bluthen/isadore_electronics/sensor_unit_modules/thermocoupleMv2/out/thermocoupleMv2.10-pin1s.png

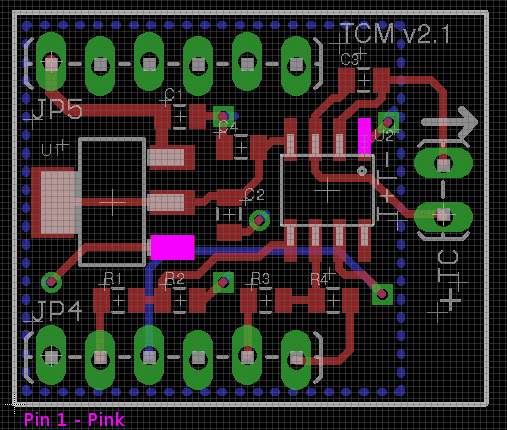
sensor_unit_modules/thermocoupleMv2/out/thermocoupleMv2.10-pin1s.png
