bluthen/isadore_electronics/sensor_unit_bme280/gerbers/sensor_unit_bme280v5.10_assembled_picture.jpg

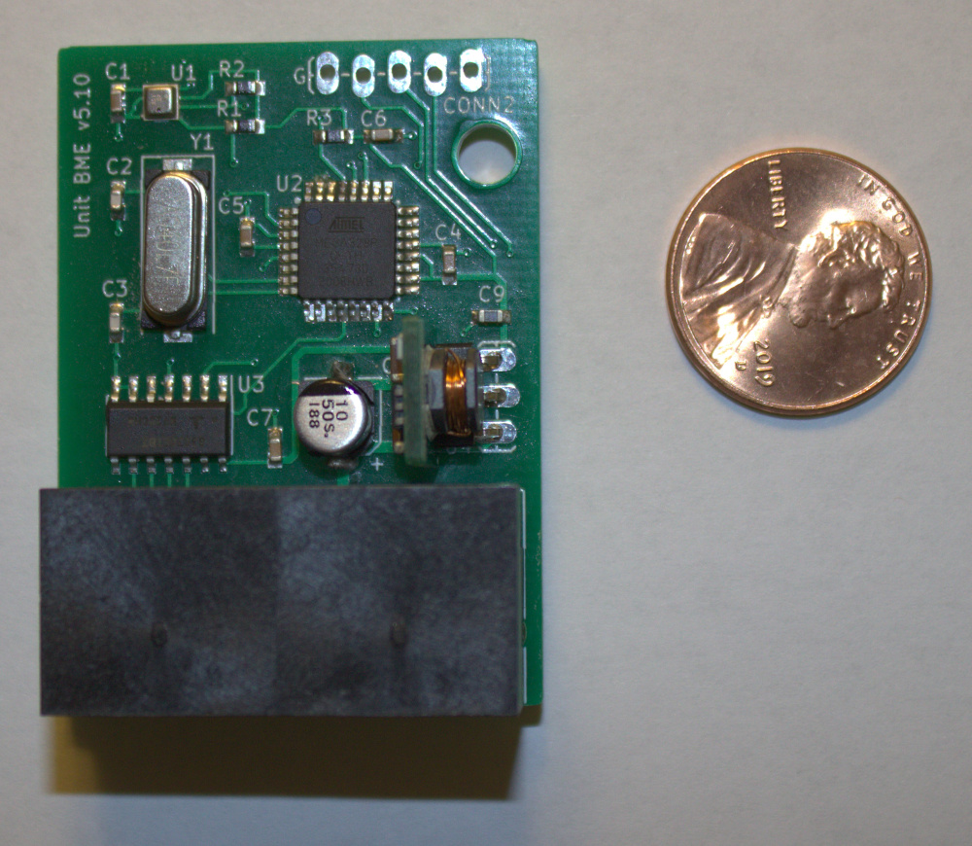
sensor_unit_bme280/gerbers/sensor_unit_bme280v5.10_assembled_picture.jpg
