bluthen/isadore_electronics/dryermaster/spitest.py

import pydev

#!/usr/bin/env python
#
# Bitbang'd SPI interface with an MCP3008 ADC device
# MCP3008 is 8-channel 10-bit analog to digital converter
#  Connections are:
#     CLK => SCLK  
#     DOUT =>  MISO
#     DIN => MOSI
#     CS => CE0

import time
import sys
import spidev
from RPi.GPIO as GPIO

rx4_20
csrx4_20=7  # In Mikro slot 2
cstx4_20=8  # In mikro slot 1

GPIO.setmode(GPIO.BCM)
GPIO.setup(csrx4_20, GPIO.OUT)
GPIO.setup(cstx4_20, GPIO.OUT)

GPIO.output(cstx4_20, GPIO.LOW)
GPIO.output(csrx4_20, GPIO.LOW)

spi = spidev.SpiDev()
spi.open(0,0)

def buildReadCommand(channel):
    startBit = 0x01
    singleEnded = 0x08

    # Return python list of 3 bytes
    #   Build a python list using [1, 2, 3]
    #   First byte is the start bit
    #   Second byte contains single ended along with channel #
    #   3rd byte is 0
    return []
    
def processAdcValue(result):
    '''Take in result as array of three bytes. 
       Return the two lowest bits of the 2nd byte and
       all of the third byte'''
    pass
        
def readAdc(channel):
    if ((channel > 7) or (channel < 0)):
        return -1
    r = spi.xfer2(buildReadCommand(channel))
    return processAdcValue(r)
        
if __name__ == '__main__':
    try:
        while True:
            val = readAdc(0)
            print "ADC Result: ", str(val)
            time.sleep(5)
    except KeyboardInterrupt:
        spi.close() 
        sys.exit(0)
